kverbeeck/IoT_House_v2/BLYNK Screenshots/1 or more ESP32 offline.PNG

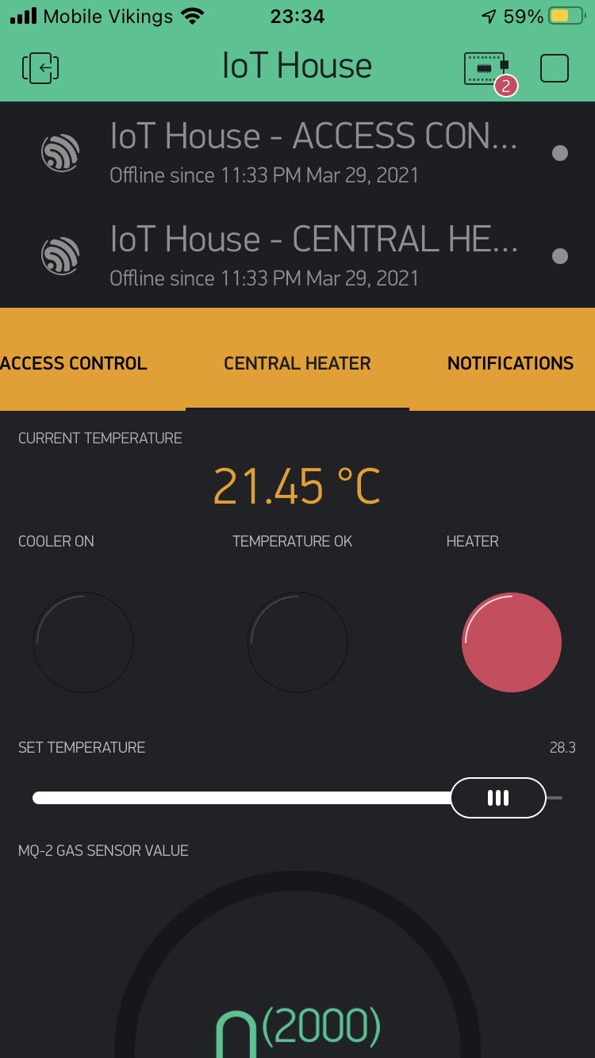
BLYNK Screenshots/1 or more ESP32 offline.PNG
