kverbeeck/IoT_House_v2/BLYNK Screenshots/Access Control for door - Config.PNG

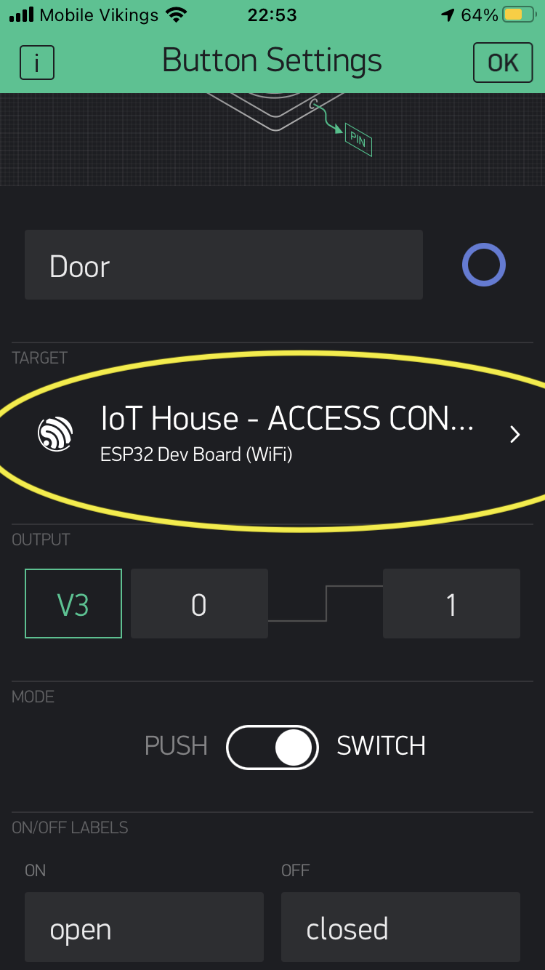
BLYNK Screenshots/Access Control for door - Config.PNG
