kverbeeck/IoT_House_v2/BLYNK Screenshots/Add the Tabs Widget first.jpg

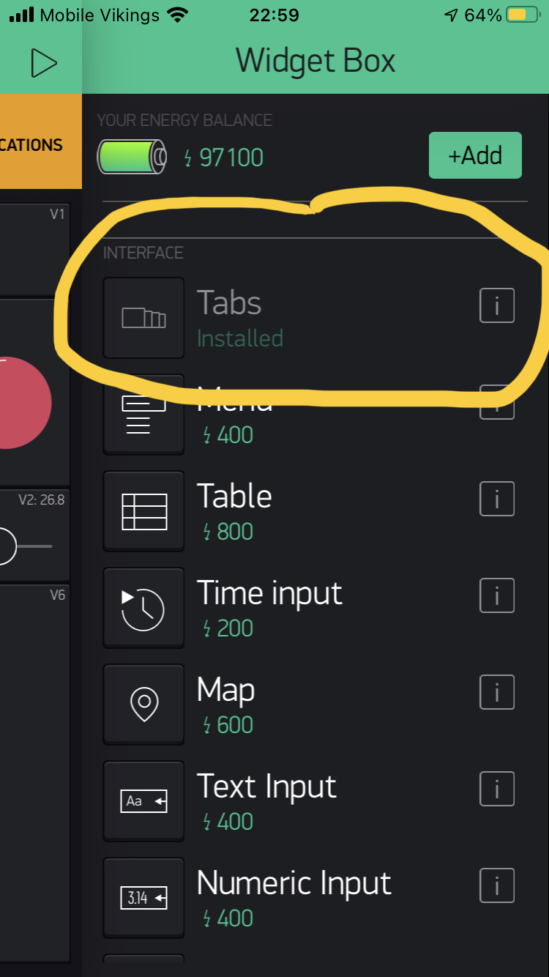
BLYNK Screenshots/Add the Tabs Widget first.jpg
