kverbeeck/IoT_House_v2/BLYNK Screenshots/Cooler LED - Config.PNG

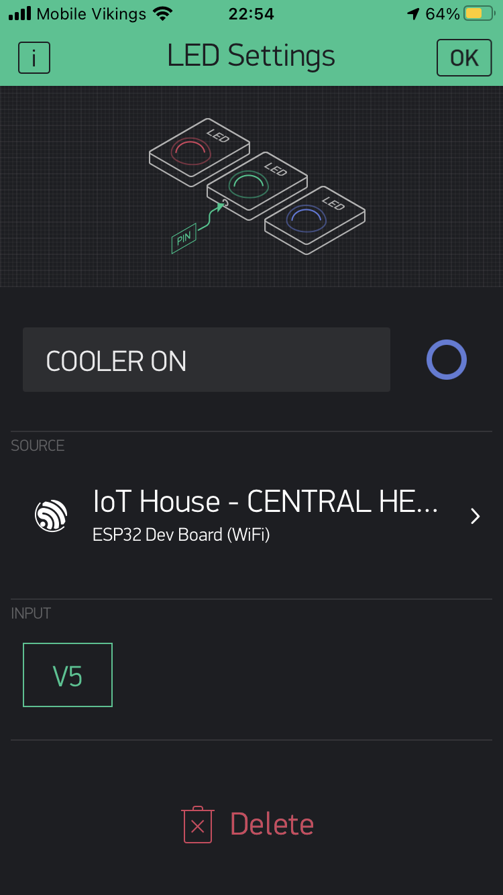
BLYNK Screenshots/Cooler LED - Config.PNG
