kverbeeck/IoT_House_v2/BLYNK Screenshots/Current Temperature - Config.PNG

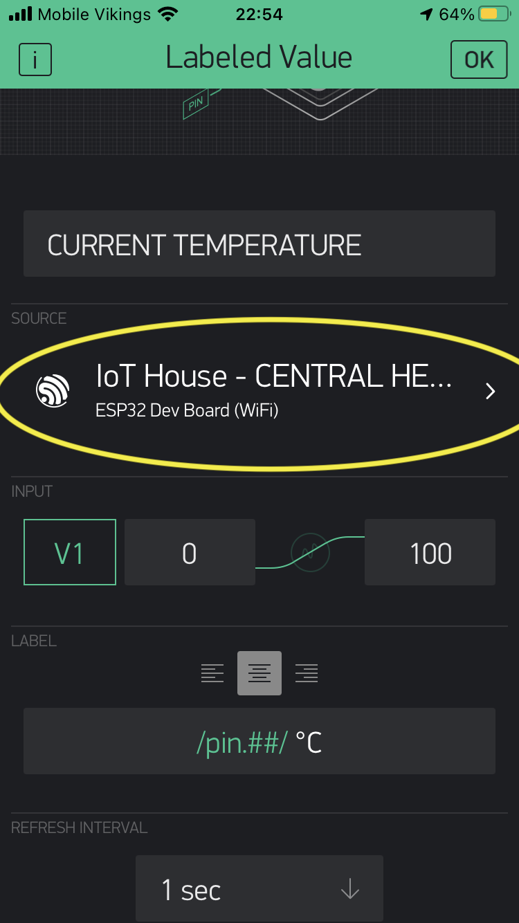
BLYNK Screenshots/Current Temperature - Config.PNG
