kverbeeck/IoT_House_v2/BLYNK Screenshots/ESP32 - 1 - Config.jpg

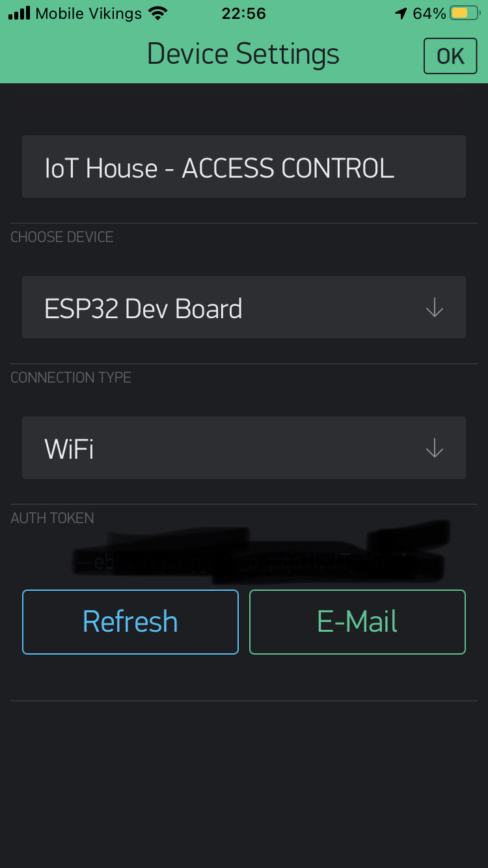
BLYNK Screenshots/ESP32 - 1 - Config.jpg
