kverbeeck/IoT_House_v2/BLYNK Screenshots/ESP32 Devices - Config.PNG

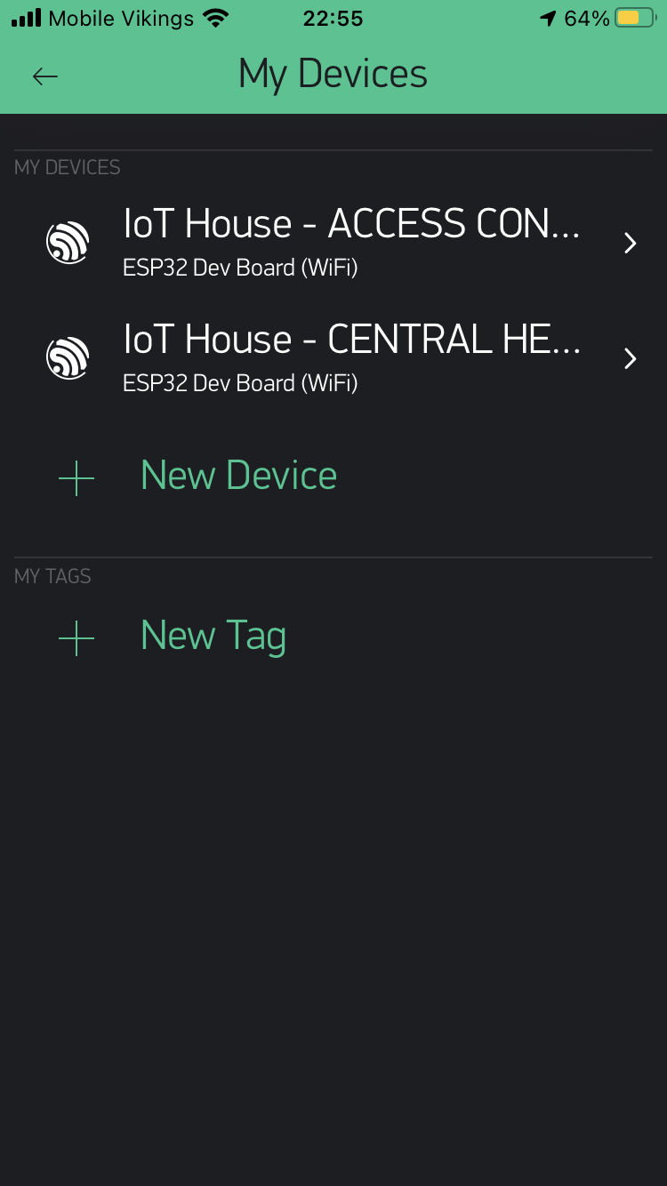
BLYNK Screenshots/ESP32 Devices - Config.PNG
