kverbeeck/IoT_House_v2/BLYNK Screenshots/How it should look - 2 ESP32s connected to server.PNG

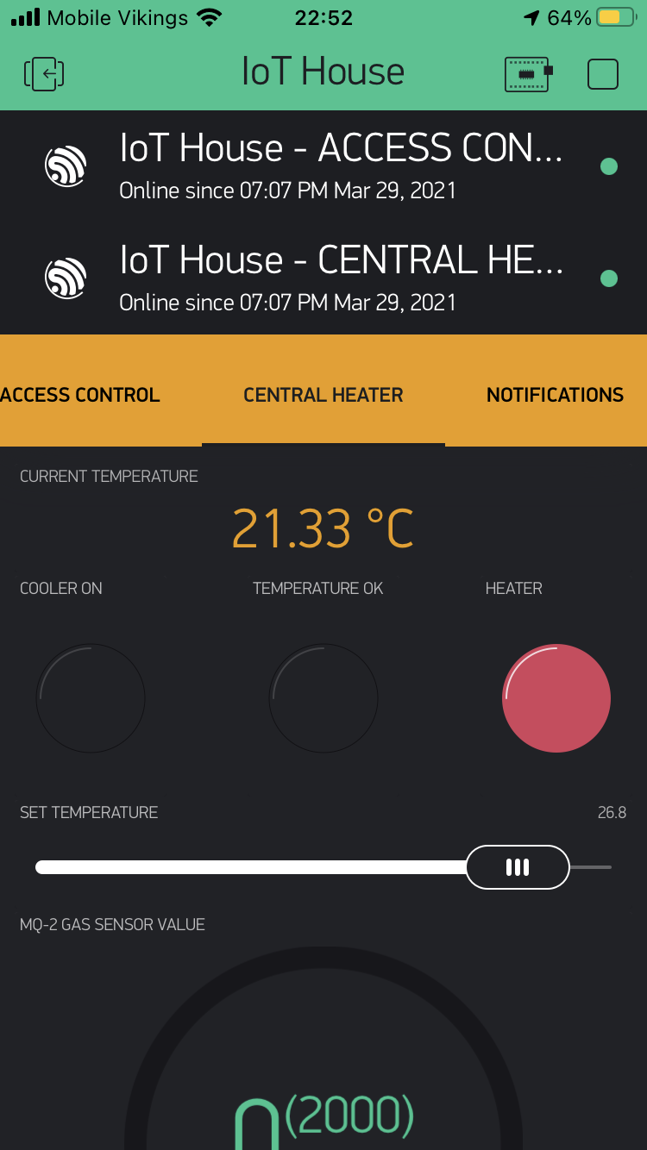
BLYNK Screenshots/How it should look - 2 ESP32s connected to server.PNG
