kverbeeck/IoT_House_v2/BLYNK Screenshots/How it should look - Access Control for door .PNG

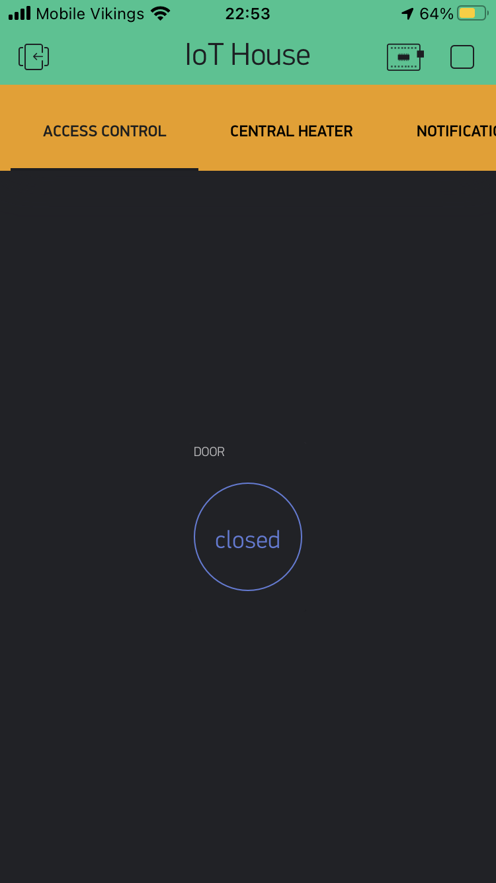
BLYNK Screenshots/How it should look - Access Control for door .PNG
