kverbeeck/IoT_House_v2/BLYNK Screenshots/How it should look - CENTRAL HEATER Tab.PNG

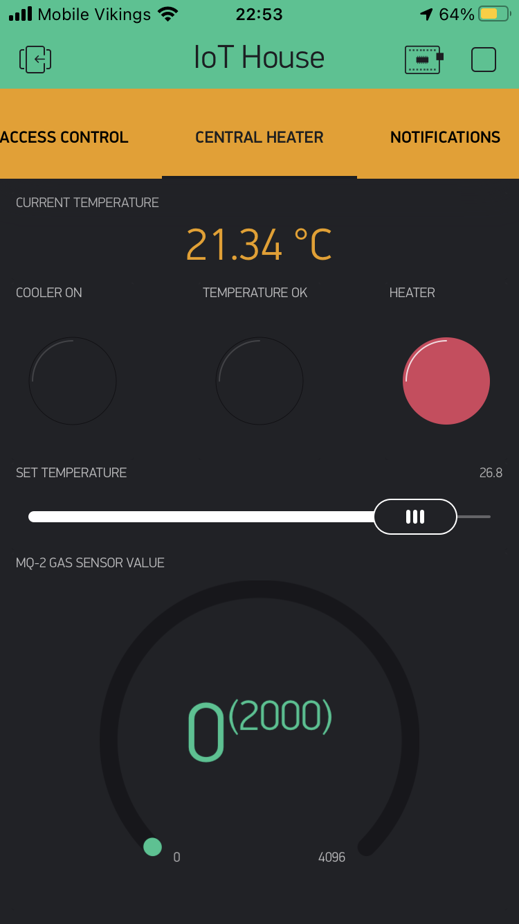
BLYNK Screenshots/How it should look - CENTRAL HEATER Tab.PNG
