kverbeeck/IoT_House_v2/BLYNK Screenshots/How it should look - Notifications.PNG

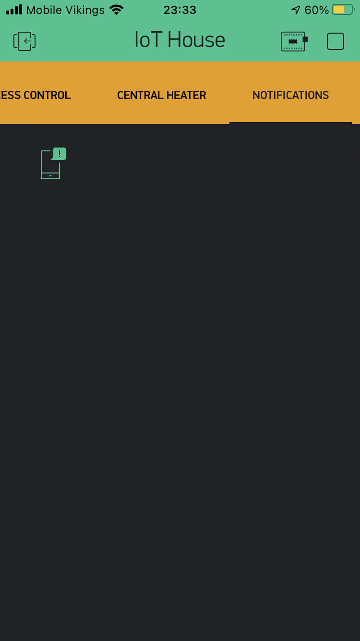
BLYNK Screenshots/How it should look - Notifications.PNG
