kverbeeck/IoT_House_v2/BLYNK Screenshots/How it should look - Tabs Widget.jpg

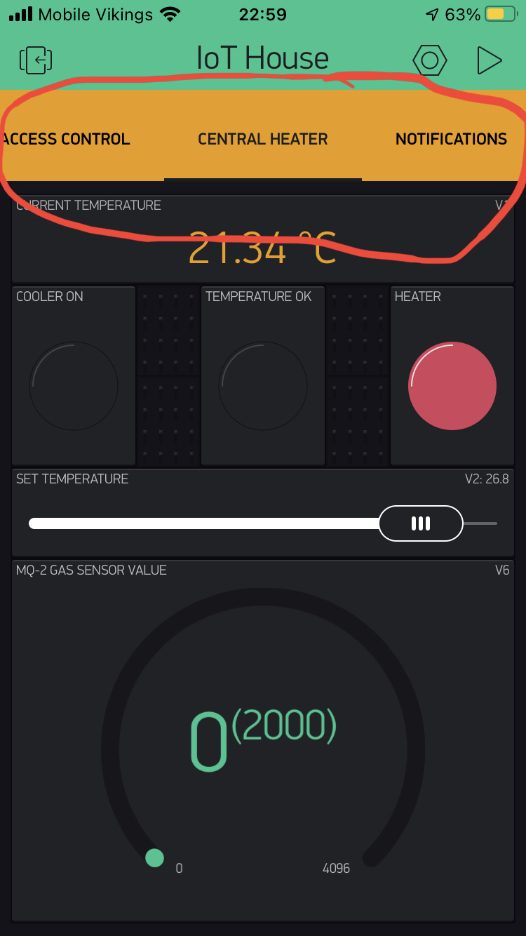
BLYNK Screenshots/How it should look - Tabs Widget.jpg
