kverbeeck/IoT_House_v2/BLYNK Screenshots/MQ-2 GAS Sensor Value - Config.PNG

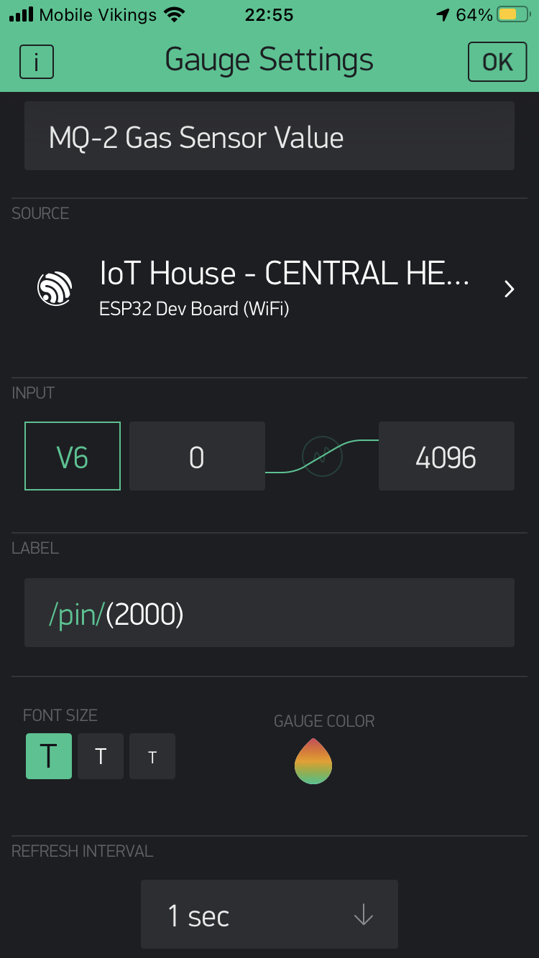
BLYNK Screenshots/MQ-2 GAS Sensor Value - Config.PNG
