kverbeeck/IoT_House_v2/BLYNK Screenshots/No connection to the BLYNK SERVER.PNG

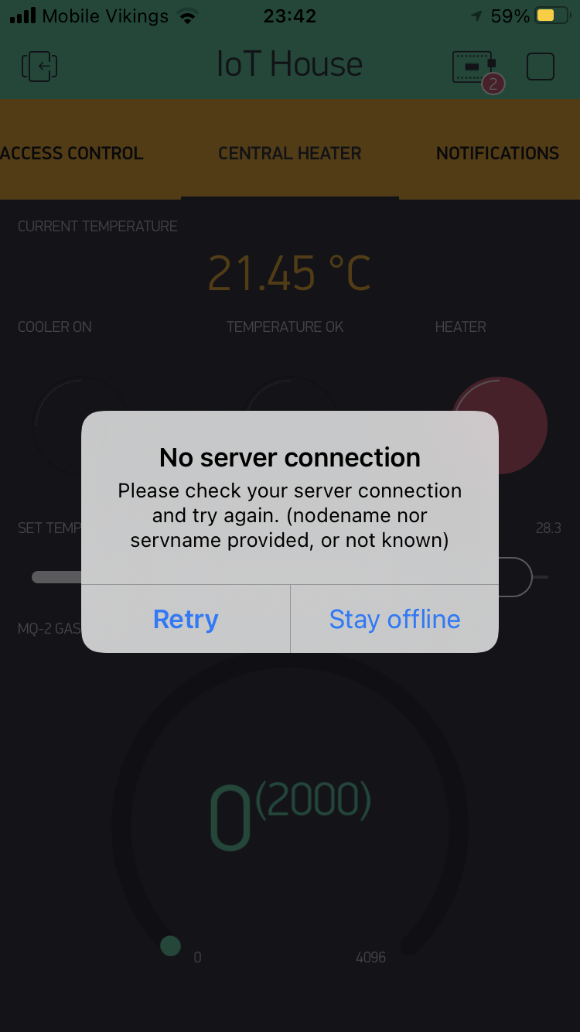
BLYNK Screenshots/No connection to the BLYNK SERVER.PNG
