kverbeeck/IoT_House_v2/BLYNK Screenshots/Notifications - Config.PNG

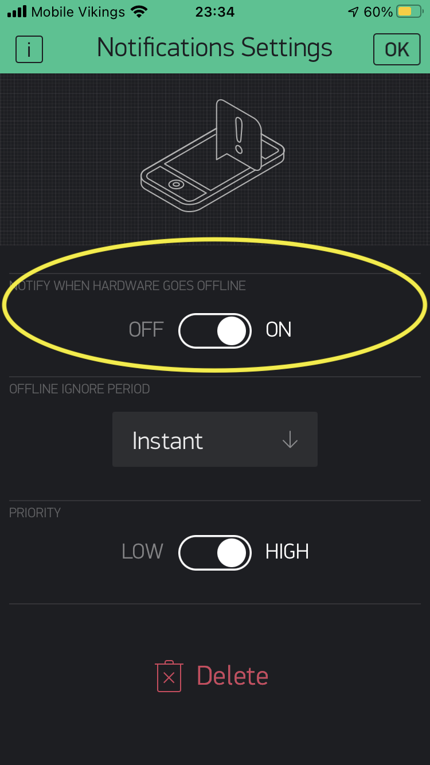
BLYNK Screenshots/Notifications - Config.PNG
