kverbeeck/IoT_House_v2/BLYNK Screenshots/Project settings - Config.PNG

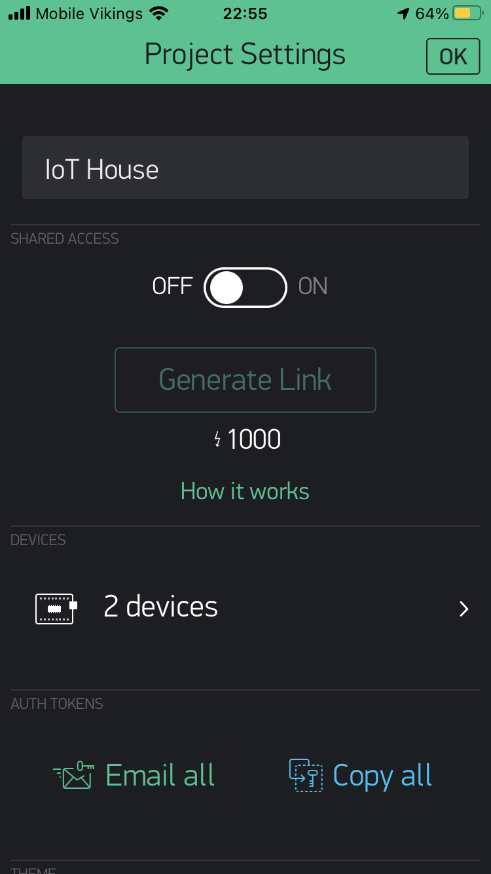
BLYNK Screenshots/Project settings - Config.PNG
