kverbeeck/IoT_House_v2/BLYNK Screenshots/Set Temperature - Config.PNG

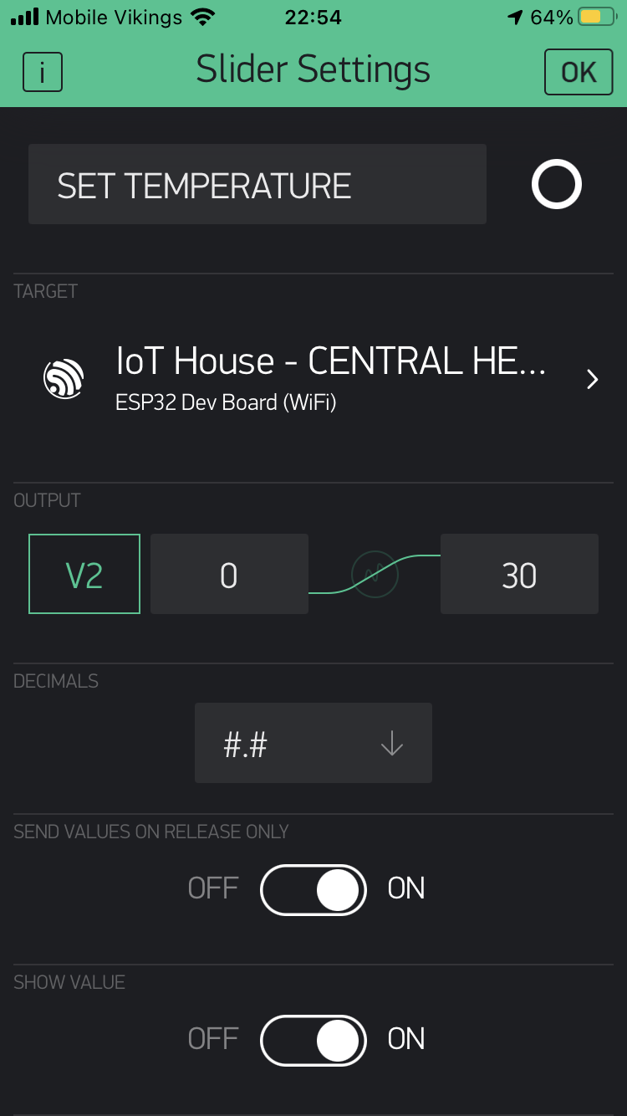
BLYNK Screenshots/Set Temperature - Config.PNG
