kverbeeck/IoT_House_v2/Photos/IMG_9255.jpg

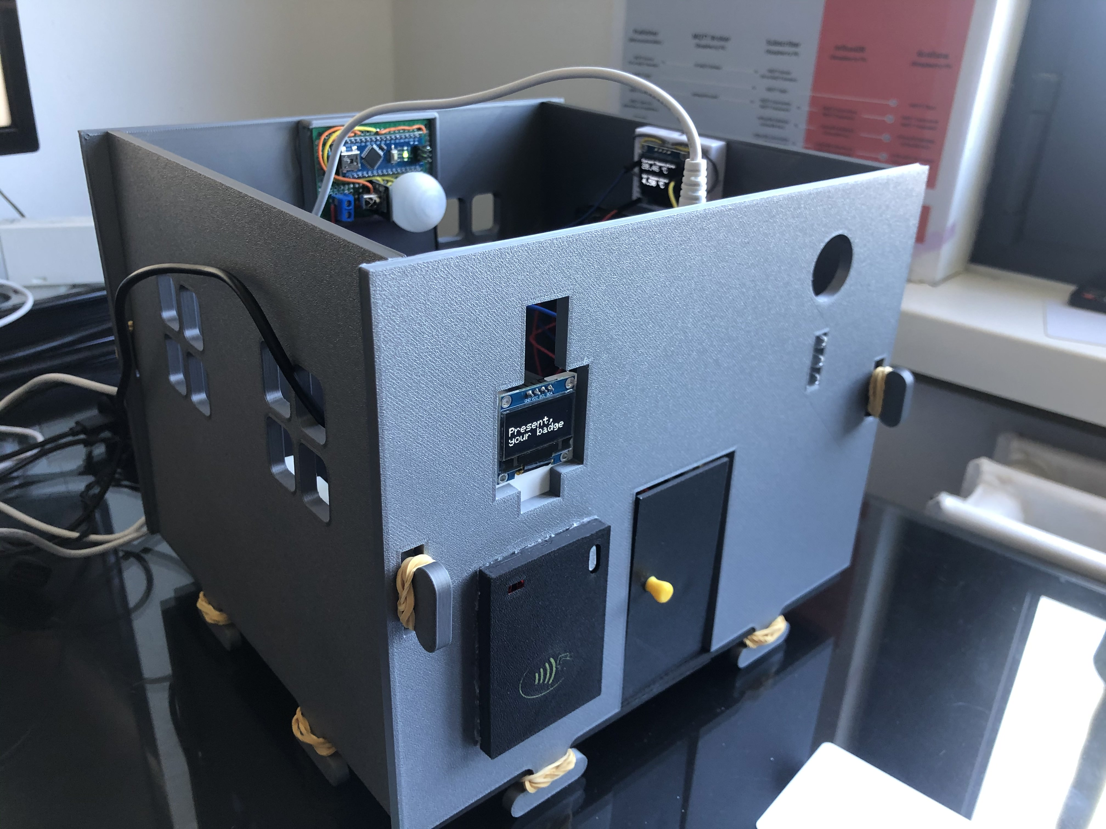
Photos/IMG_9255.jpg
