kverbeeck/IoT_House_v2/Photos/IMG_9256.jpg

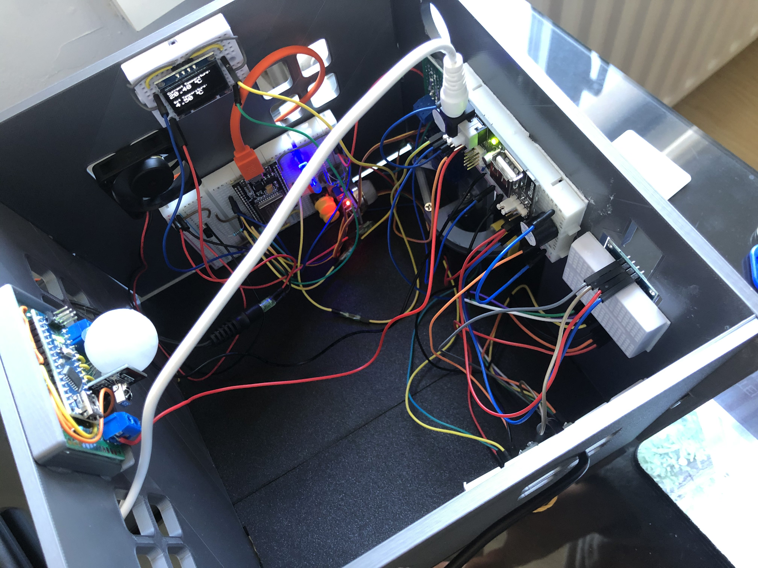
Photos/IMG_9256.jpg
