kverbeeck/IoT_House_v2/Photos/IMG_9262.jpg

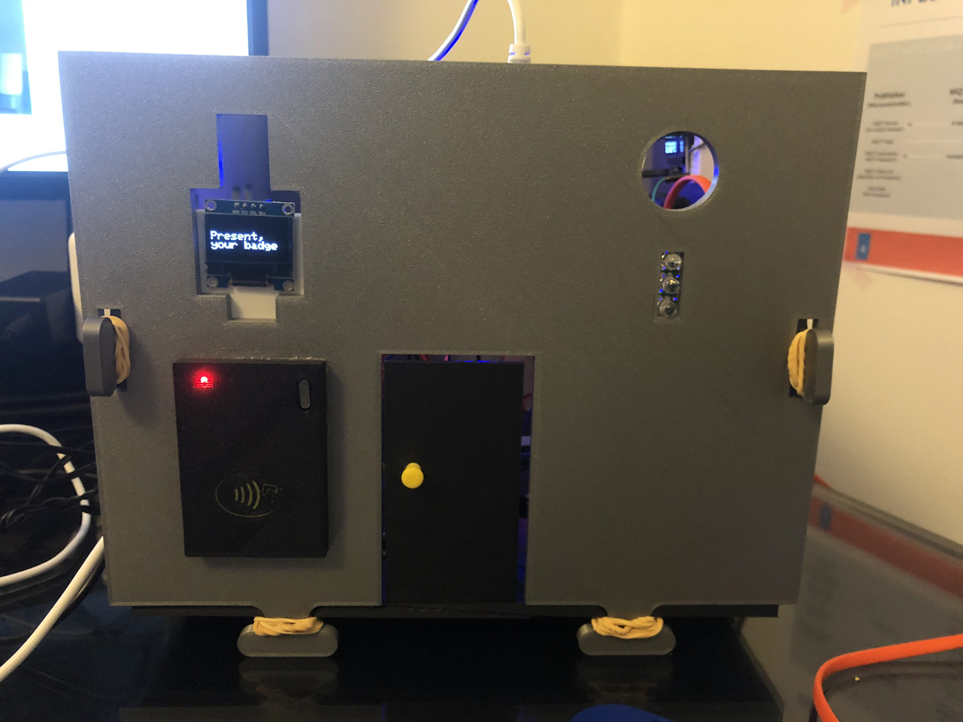
Photos/IMG_9262.jpg
