kverbeeck/IoT_House_v2/Photos/IMG_9263.jpg

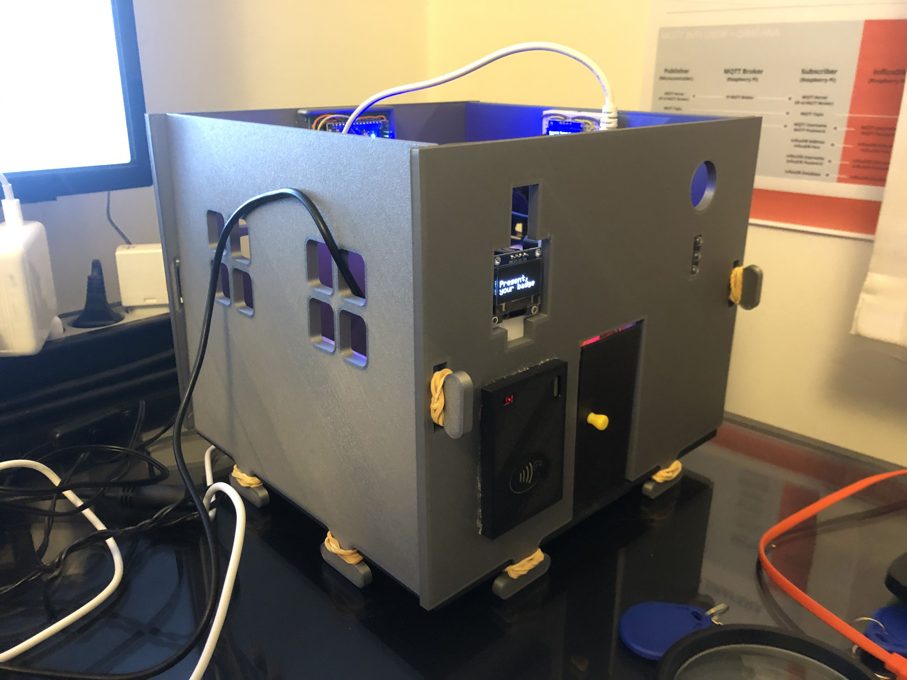
Photos/IMG_9263.jpg
