kverbeeck/IoT_House_v2/Photos/IMG_9264.jpg

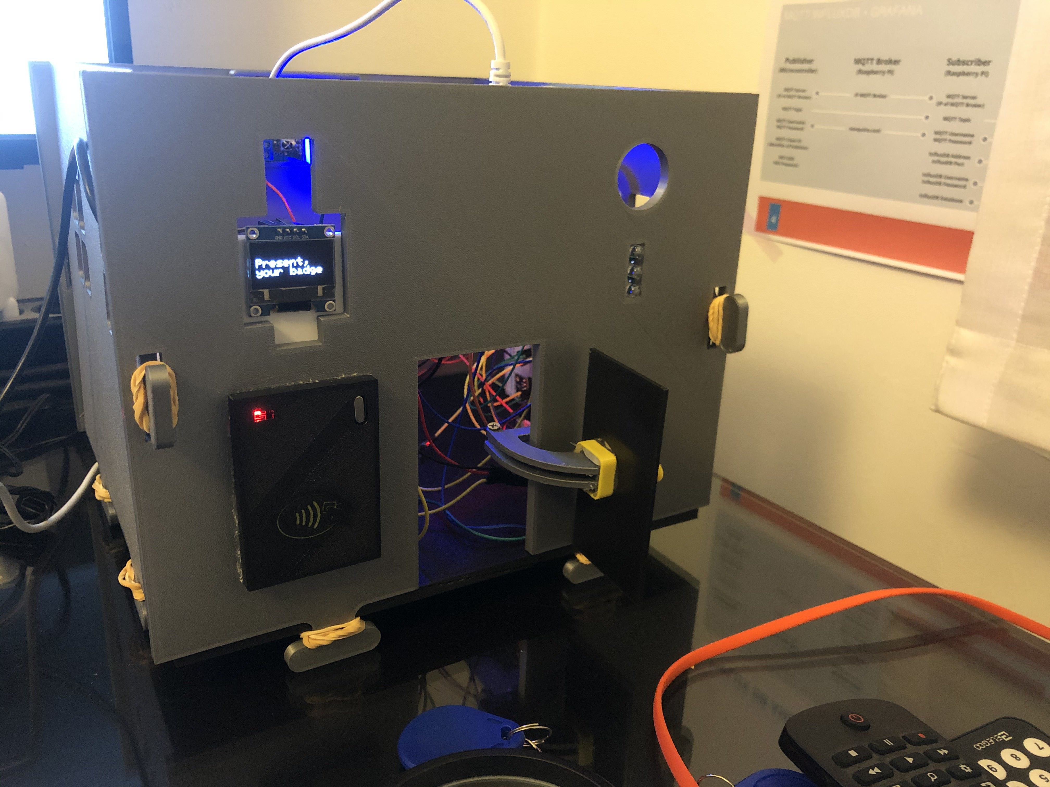
Photos/IMG_9264.jpg
