kverbeeck/IoT_House_v2/Photos/IMG_9265.jpg

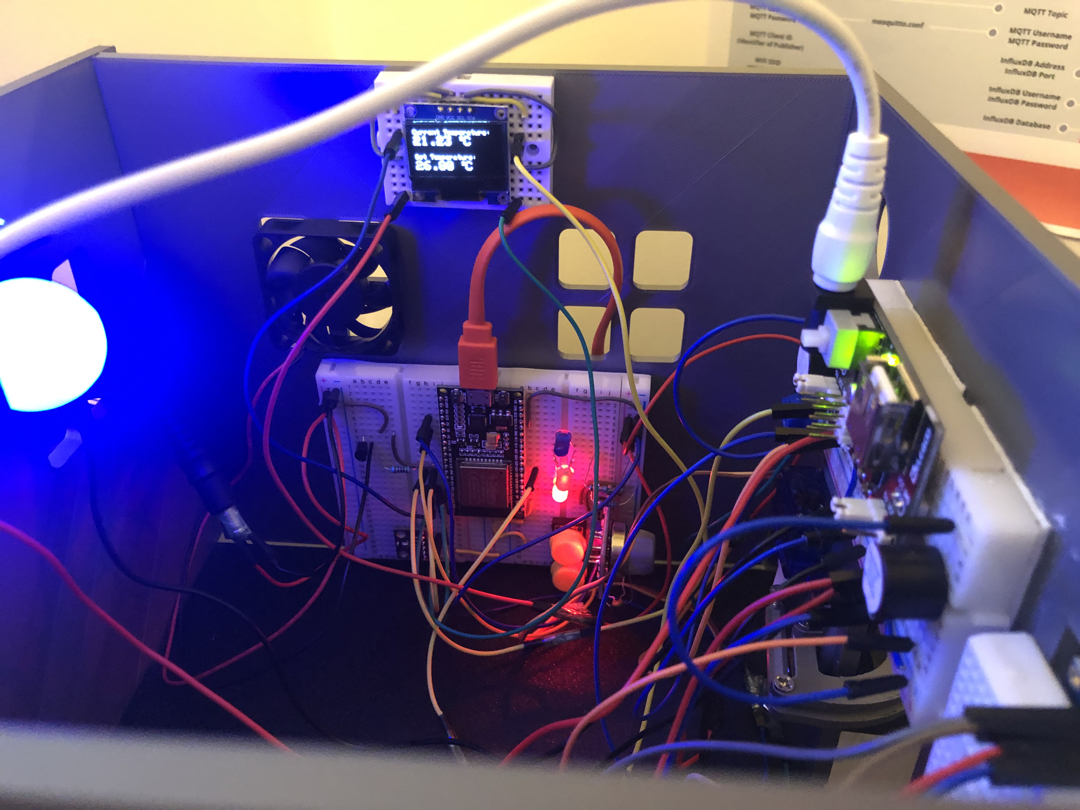
Photos/IMG_9265.jpg
