kverbeeck/IoT_House_v2/Photos/IMG_9267.jpg

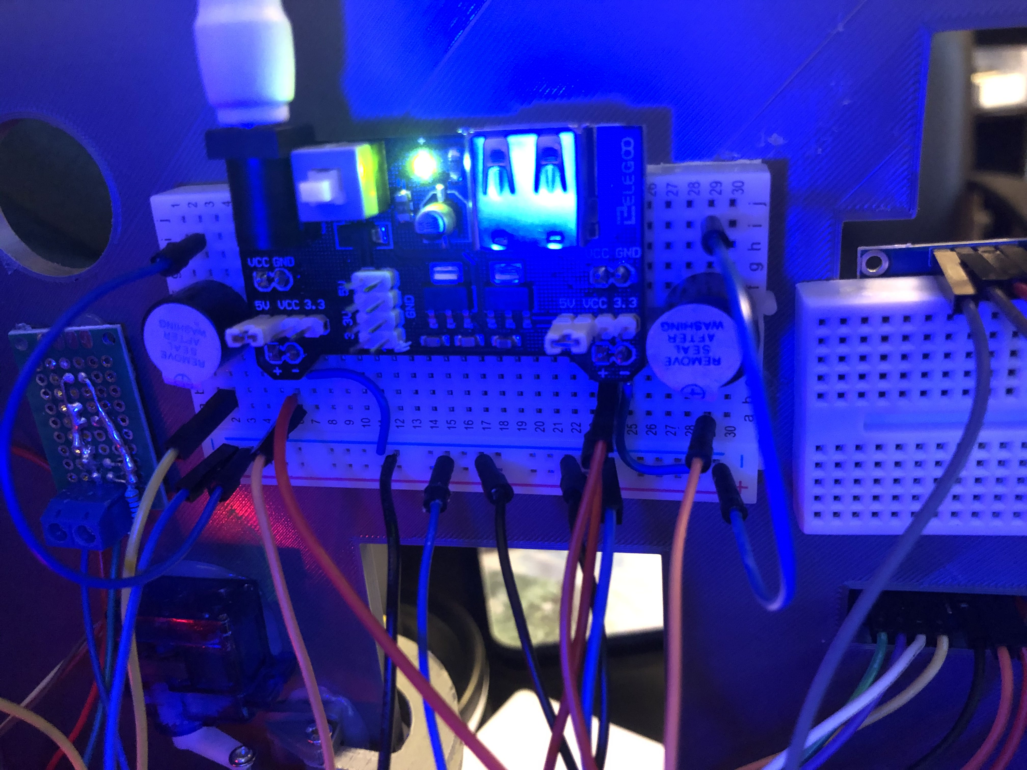
Photos/IMG_9267.jpg
