kverbeeck/IoT_House_v2/Photos/IMG_9268.jpg

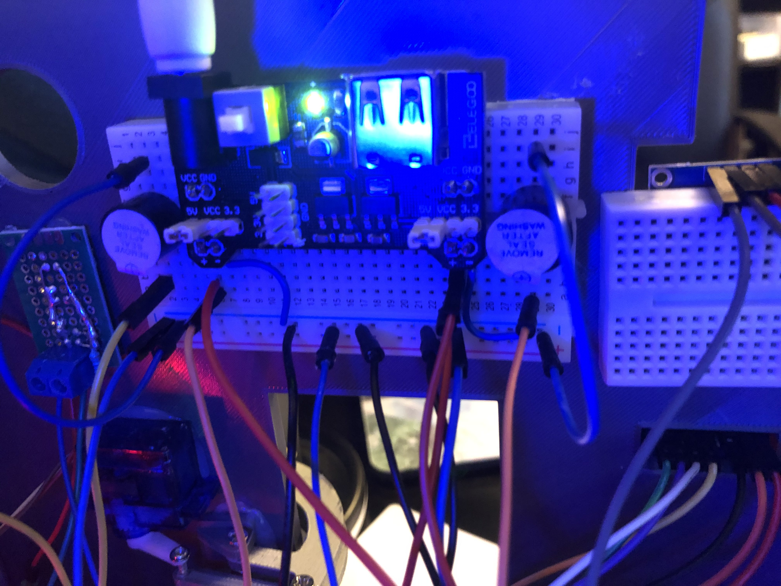
Photos/IMG_9268.jpg
