kverbeeck/IoT_House_v2/Photos/IMG_9269.jpg

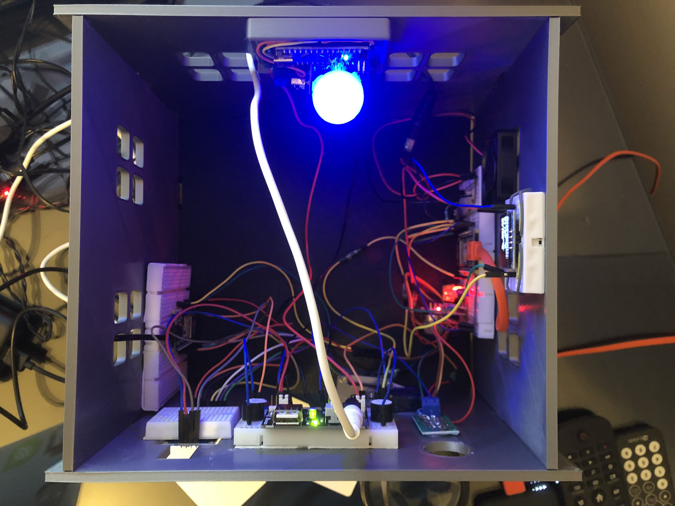
Photos/IMG_9269.jpg
