kverbeeck/IoT_House_v2/Photos/IMG_9270.jpg

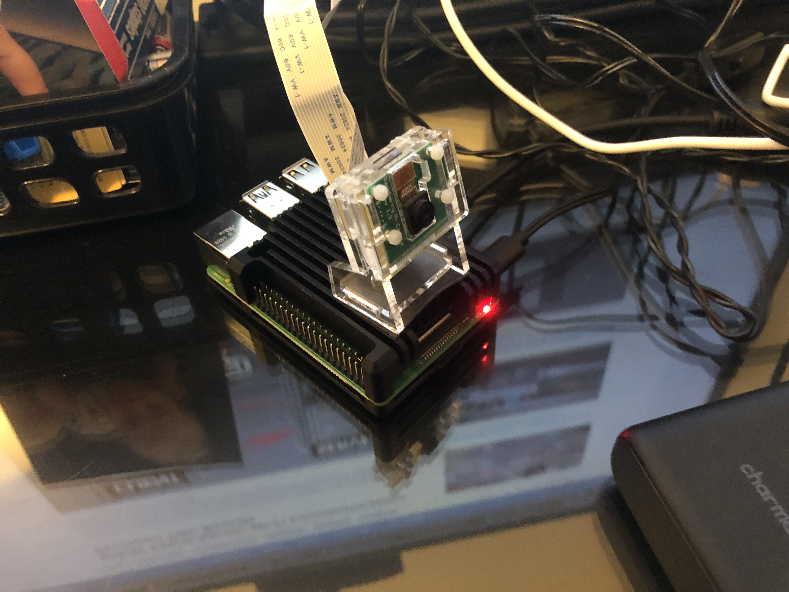
Photos/IMG_9270.jpg
