kverbeeck/IoT_House_v2/Photos/IMG_9272.jpg

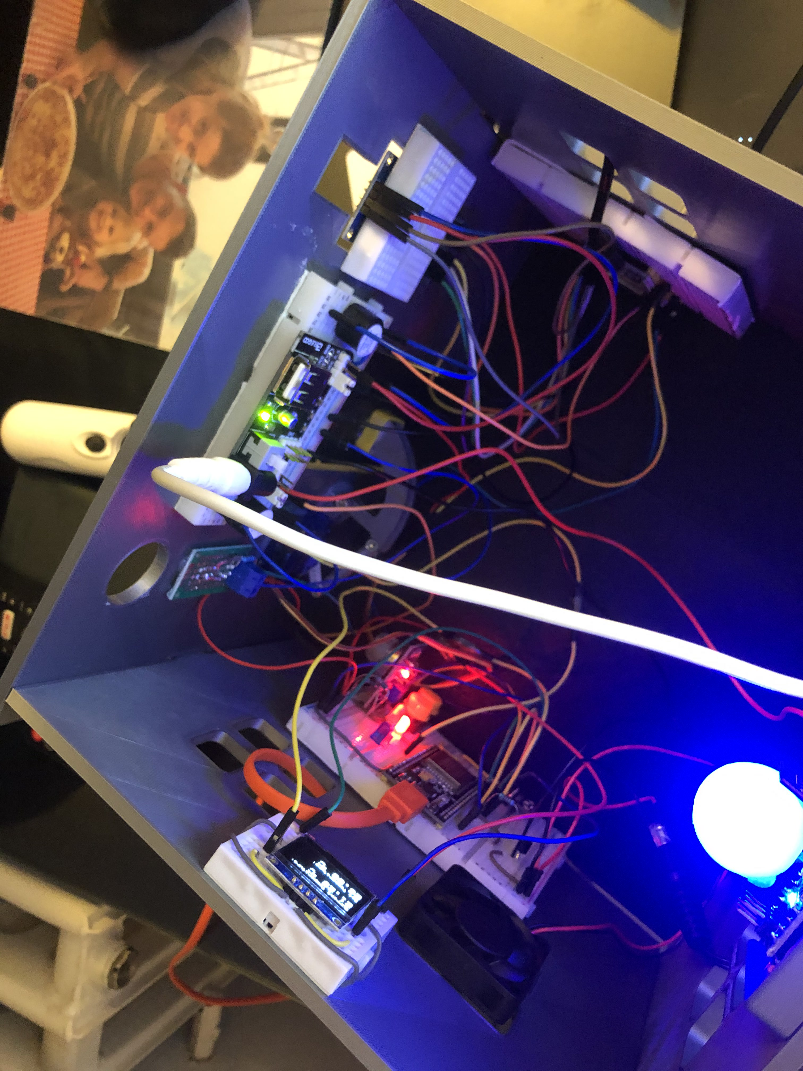
Photos/IMG_9272.jpg
